AndreaLoGiudice/Double-Branch-Dickson-Charge-Pump/Simulation/cockcroft.asc

C1: cap; 2.2µf
C2: cap; 2.2µf
C3: cap; 2.2µf
C4: cap; 100µ
D1: diode; 1N4148
D2: diode; 1N4148
D3: diode; 1N4148
D4: diode; 1N4148
R1: res; 12k
V1: voltage; 3.3
V2: voltage; PULSE(0 3.3 0 10n 10n 500u 1m)
V3: voltage; PULSE(0 3.3 500u 10n 10n 500u 1m)
Named nets: 0
.tran 1
