AndreaLoGiudice/Double-Branch-Dickson-Charge-Pump/Simulation/dickson_double.asc

C1: cap; 1.1µF
C2: cap; 1.1µF
C3: cap; 1.1µF
C4: cap; 1.1µF
C5: cap; 1.1µF
C6: cap; 1.1µF
C7: cap; 1.1µF
C8: cap; 1.1µF
C9: cap; 1.1µF
C10: cap; 100µ
D1: diode; 1N4148
D2: diode; 1N4148
D3: diode; 1N4148
D4: diode; 1N4148
D5: diode; 1N4148
D6: diode; 1N4148
D7: diode; 1N4148
D8: diode; 1N4148
D9: diode; 1N4148
D10: diode; 1N4148
R1: res; 12k
V1: voltage; 3.3
V2: voltage; PULSE(0 3.3 0 10n 10n 500u 1m)
V3: voltage; PULSE(0 3.3 500u 10n 10n 500u 1m)
Named nets: 0, CK, CK_INV
.tran 3
