AndreaLoGiudice/Double-Branch-Dickson-Charge-Pump/Simulation/simulazione_chip_buffer.asc

C1: cap; 1.1µF
C2: cap; 2.2µF
C3: cap; 2.2µF
C4: cap; 2.2µF
C5: cap; 2.2µF
C6: cap; 2.2µF
C7: cap; 2.2µF
C8: cap; 2.2µF
C9: cap; 2.2µF
C10: cap; 100µ
D1: schottky; BAT54
D2: schottky; BAT54
D3: schottky; BAT54
D4: schottky; BAT54
D5: schottky; BAT54
D6: schottky; BAT54
D7: schottky; BAT54
D8: schottky; BAT54
D9: schottky; BAT54
D10: schottky; BAT54
R1: res; 12k
R2: res; 47
R3: res; 45
R4: res; 25
R5: res; 25
V1: voltage; 3.3
V2: voltage; PULSE(0 3.3 0 10n 10n 500u 1m)
V3: voltage; PULSE(0 3.3 500u 10n 10n 500u 1m)
Named nets: 0, CK, CK_INV, VIN, CKI, CKNI
.tran 2
.meas TRAN Pvin AVG (-V(VIN)*I(V1)) FROM 450m TO 500m
.meas TRAN Pck  AVG (-V(CKI)*I(V2)) FROM 450m TO 500m
.meas TRAN Pckn AVG (-V(CKNI)*I(V3)) FROM 450m TO 500m
